cwi-dis/lissabon/python/sandbox/testlux.csv

requested | w_white | rgb_white | rgbw_white | rgb_r | rgb_g | rgb_b | w_lux | rgb_lux | rgbw_lux | w_cct | rgb_cct | rgbw_cct | parameter | value
0.0 | 0.065064 | 0.065019 | 0.065095 | 0.013901 | 0.009506 | 0.004196 | 19.44228 | 19.59958 | 19.59958 | 2511 | 2538 | 2524
0.0625 | 0.065049 | 0.065095 | 0.064958 | 0.013993 | 0.009567 | 0.004257 | 19.53666 | 19.72542 | 19.6625 | 2521 | 2545 | 2538
0.125 | 0.069169 | 0.068269 | 0.064408 | 0.01619 | 0.011307 | 0.005905 | 24.57026 | 23.31186 | 19.47374 | 2661 | 2790 | 2531
0.1875 | 0.077455 | 0.074586 | 0.06746 | 0.020645 | 0.015167 | 0.008988 | 35.3925 | 31.27124 | 23.50062 | 2871 | 3181 | 2698
0.25 | 0.087846 | 0.082399 | 0.070359 | 0.026352 | 0.020066 | 0.012955 | 48.66862 | 41.3699 | 28.03086 | 3026 | 3527 | 2906
0.3125 | 0.104891 | 0.095247 | 0.077134 | 0.035401 | 0.027909 | 0.019425 | 70.18726 | 57.54034 | 36.9655 | 3155 | 3921 | 3136
0.375 | 0.123964 | 0.109651 | 0.08365 | 0.045426 | 0.036515 | 0.026658 | 93.97102 | 75.28378 | 45.96306 | 3219 | 4205 | 3280
0.4375 | 0.149401 | 0.129046 | 0.090135 | 0.059037 | 0.048112 | 0.036133 | 126.3119 | 99.19338 | 54.77186 | 3291 | 4409 | 3394
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
