cwi-dis/lissabon/python/sb2/lux-2800-max.pdf

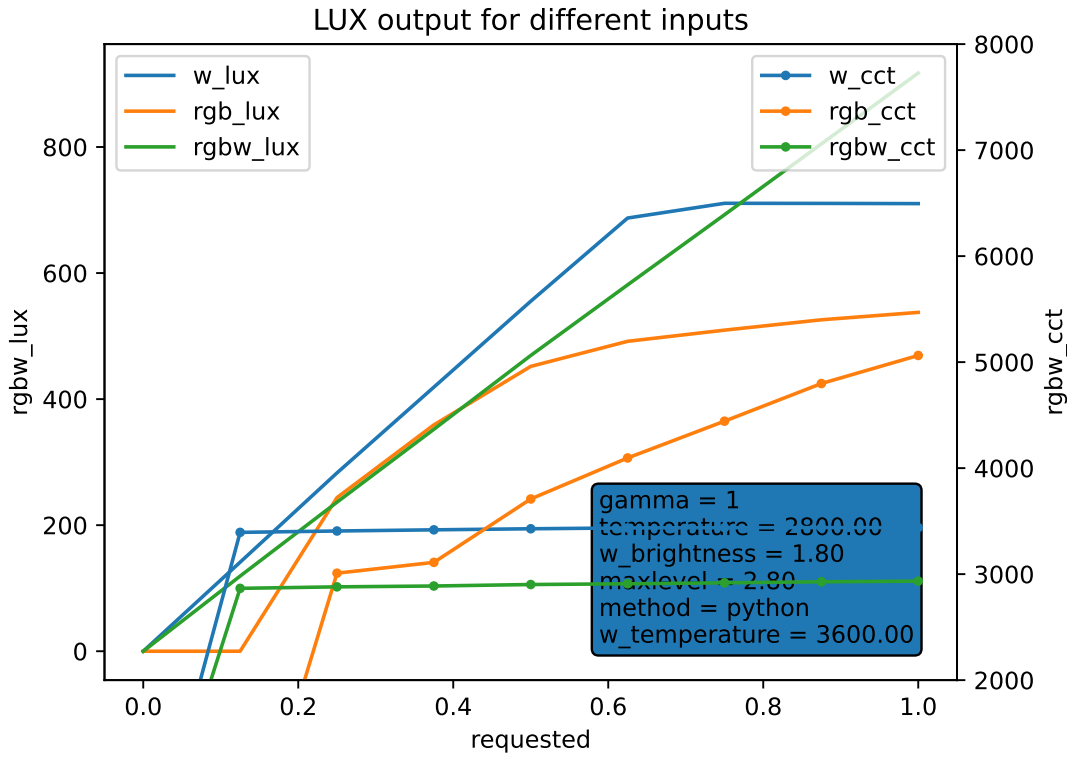
[picture p17: page 1]
requested; rgbw_lux; gamma = 1 temperature = 2800.00 w_brightness = 1.80 maxlevel = 2.80 method = python w_temperature = 3600.00; w_lux rgb_lux rgbw_lux; rgbw_cct; w_cct rgb_cct rgbw_cct

LUX output for different inputs
