cwi-dis/lissabon/python/sb2/lux-6500.pdf

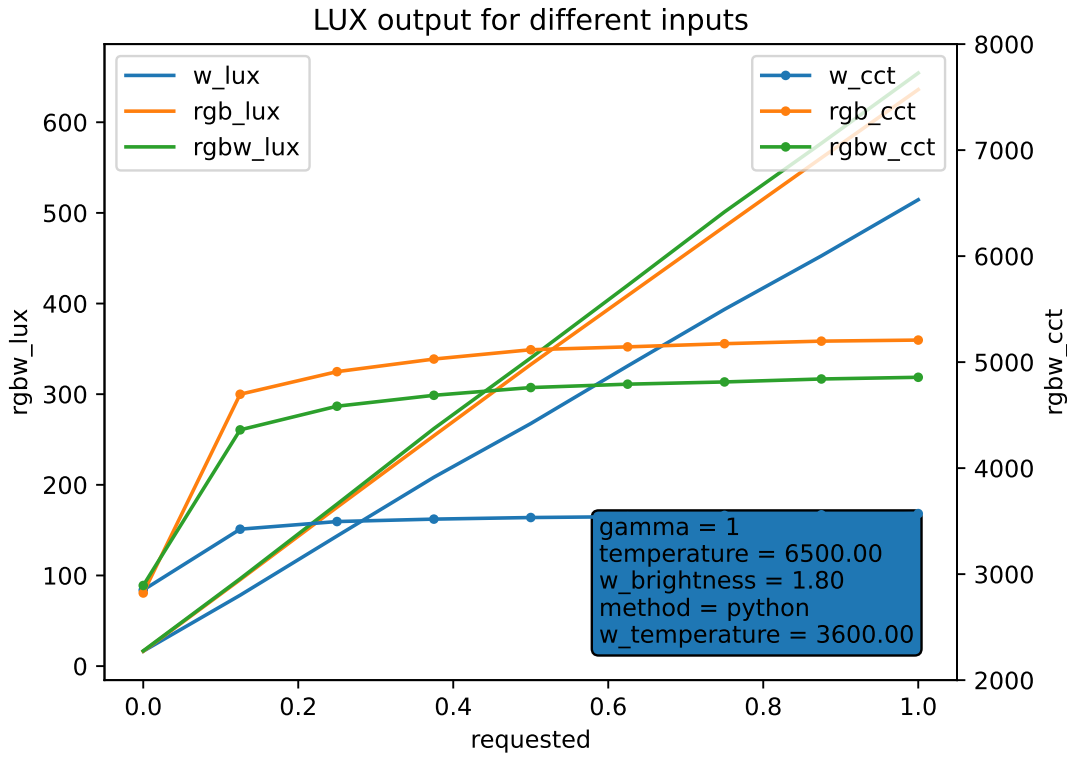
[picture p19: page 1]
requested; rgbw_lux; gamma = 1 temperature = 6500.00 w_brightness = 1.80 method = python w_temperature = 3600.00; w_lux rgb_lux rgbw_lux; rgbw_cct; w_cct rgb_cct rgbw_cct

LUX output for different inputs
