cwi-dis/lissabon/python/sb2/lux-correct.pdf

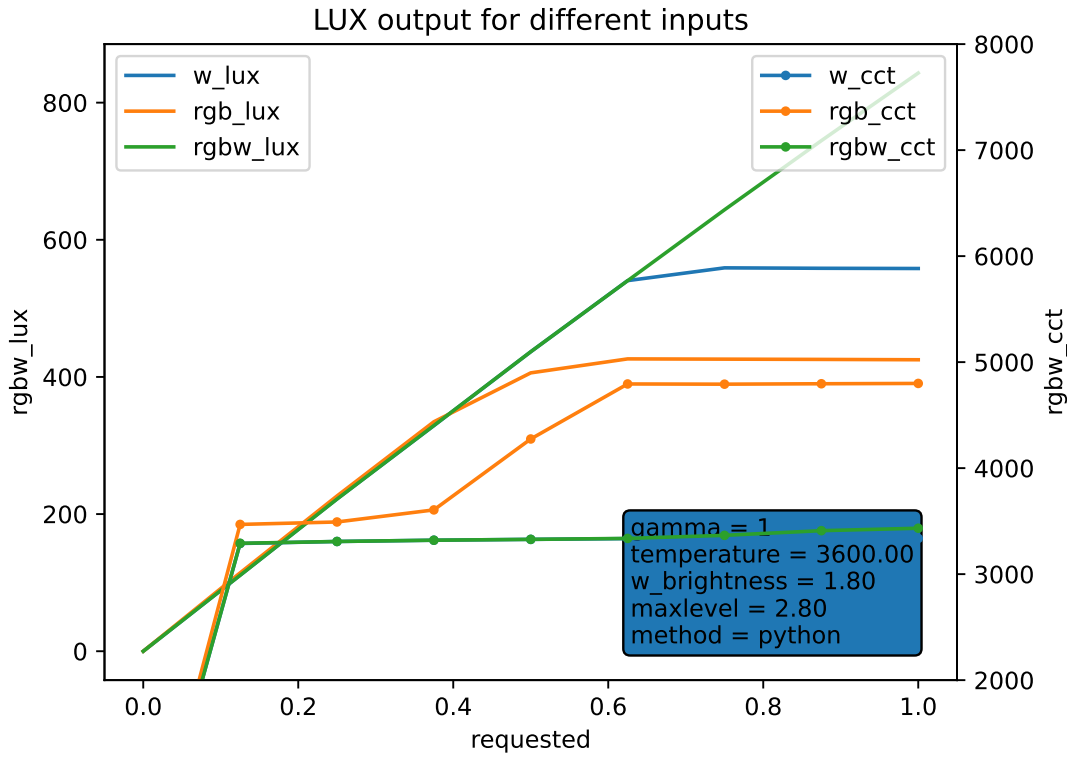
[picture p20: page 1]
requested; rgbw_lux; gamma = 1 temperature = 3600.00 w_brightness = 1.80 maxlevel = 2.80 method = python; w_lux rgb_lux rgbw_lux; rgbw_cct; w_cct rgb_cct rgbw_cct

LUX output for different inputs
