cwi-dis/lissabon/python/sb2/lux.pdf

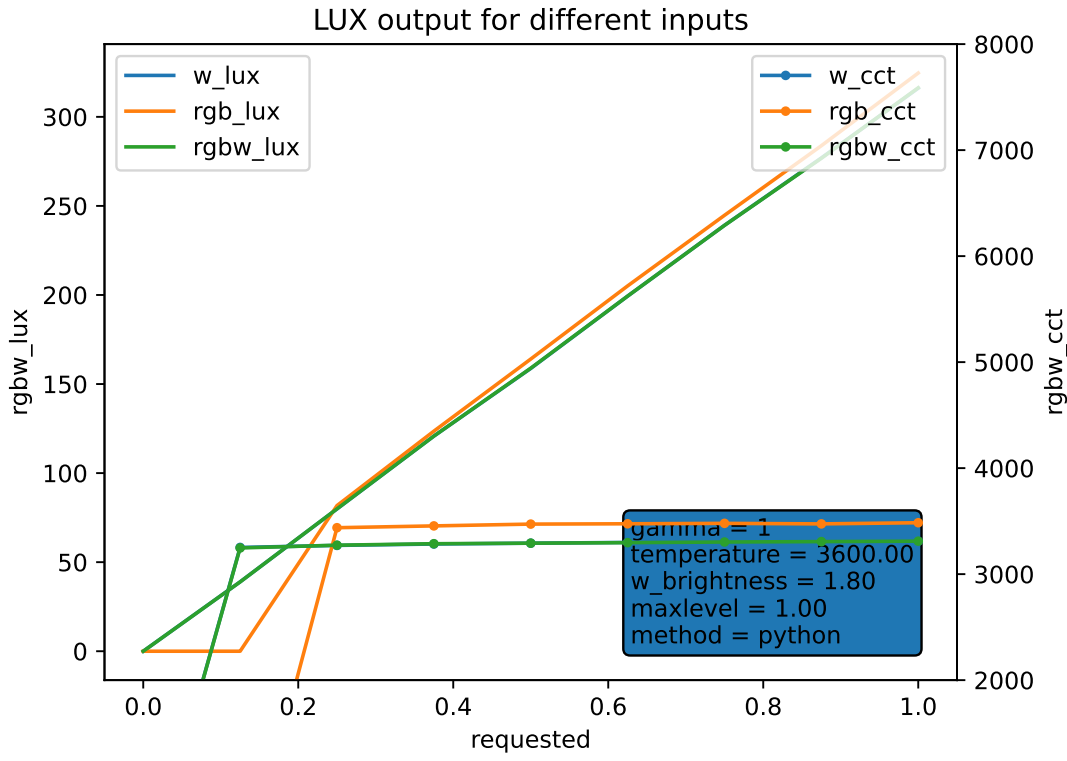
[picture p21: page 1]
requested; rgbw_lux; gamma = 1 temperature = 3600.00 w_brightness = 1.80 maxlevel = 1.00 method = python; w_lux rgb_lux rgbw_lux; rgbw_cct; w_cct rgb_cct rgbw_cct

LUX output for different inputs
