cwi-dis/lissabon/lissabonLedstrip/lissabonLedstrip.cpp

//
// A Neopixel strip server, which allows control over a strip of neopixels, intended
// to be used as lighting. Color can be set as fraction RGB or HSL, gamma can be changed,
// interval between lit pixels can be changed. Control is through a web UI or
// through REST calls (and/or, depending on Iotsa compile time options, COAP calls).
// The web interface can be disabled by building iotsa with IOTSA_WITHOUT_WEB.
//

#include "iotsa.h"
#include "iotsaConfigFile.h"
#include "LedstripDimmer.h"
#include "DimmerUI.h"

//
// Device can be rebooted or configuration mode can be requested by quickly tapping any button.
// TAP_DURATION sets the maximum time between press-release-press-etc.
#define TAP_COUNT_MODE_CHANGE 3
#define TAP_COUNT_REBOOT 6
#define TAP_DURATION 1000

// Enable Over The Air updates from ArduinoIDE. Needs at least 1MB flash.

// Define this to enable support for touchpads to control the led strip (otherwise only BLE/REST/WEB control)
#define WITH_TOUCHPADS

IotsaApplication application("Lissabon LEDstrip");

#ifdef IOTSA_WITH_BLE
#else
#warning Building this module without BLE support may be a bit pointless
#endif

#include "iotsaBattery.h"
#include "iotsaRunmode.h"
#define PIN_DISABLESLEEP 0
#define PIN_VBAT 35
#define VBAT_100_PERCENT (12.7/10.0) // 100K and 1M resistors divide by 11, not 10...
#define VBAT_0_PERCENT (10.5/10.0) // 100K and 1M resistors divide by 11, not 10...
IotsaBatteryMod batteryMod(application);

#include "iotsaPixelstrip.h"
IotsaPixelstripMod pixelstripMod(application);

#ifdef WITH_TOUCHPADS
#include "iotsaInput.h"
Touchpad upTouch(32, true, true, true);
Touchpad downTouch(13, true, true, true);
UpDownButtons levelEncoder(upTouch, downTouch, true);
Touchpad upTempTouch(14, true, true, true);
Touchpad downTempTouch(15, true, true, true);
UpDownButtons temperatureEncoder(upTempTouch, downTempTouch, false);
//Touchpad(15, true, false, true);

Input* inputs[] = {
  &levelEncoder,
  &temperatureEncoder
};

IotsaInputMod inputMod(application, inputs, sizeof(inputs)/sizeof(inputs[0]));
#endif // WITH_TOUCHPADS

#include "DimmerBLEServer.h"

using namespace Lissabon;

//
// LED Lighting module. 
//

class LissabonLedstripMod : public IotsaModule, public DimmerCallbacks
{
public:
  LissabonLedstripMod(IotsaApplication& _app)
  : IotsaModule(_app),
    dimmer(1, pixelstripMod, this),
#ifdef WITH_TOUCHPADS
    dimmerUI(dimmer),
#endif
    dimmerBLEServer(dimmer)
  {
  }
  void setup();
  void lateSetup() override;
  String info();
  void configLoad();
  void configSave();
  void loop();

protected:
  void dimmerOnOffChanged() override;
  void dimmerValueChanged() override;
  void dimmerAvailableChanged() override {};
  bool getHandler(const char *path, JsonObject& reply) override;
  bool putHandler(const char *path, const JsonVariant& request, JsonObject& reply) override;
private:
  void _tap();
  LedstripDimmer dimmer;
#ifdef WITH_TOUCHPADS
  DimmerUI dimmerUI;
#endif
  DimmerBLEServer dimmerBLEServer;
  void webHandler() override;

  uint32_t saveAtMillis = 0;
  uint32_t lastButtonChangeMillis = 0;
  int buttonChangeCount = 0;
};

void LissabonLedstripMod::_tap() {
  // Called whenever any button changed state.
  // Used to give visual feedback (led turning off) on presses and releases,
  // and to enable config mod after 4 taps and reboot after 8 taps
  uint32_t now = millis();
  if (now >= lastButtonChangeMillis + TAP_DURATION) {
    // Either the first change, or too late. Reset.
    if (lastButtonChangeMillis > 0) {
      IotsaSerial.println("TapCount: reset");
    }
    lastButtonChangeMillis = millis();
    buttonChangeCount = 0;
  }
  if (lastButtonChangeMillis > 0 && now < lastButtonChangeMillis + TAP_DURATION) {
    // A button change that was quick enough for a tap
    lastButtonChangeMillis = now;
    buttonChangeCount++;
    IFDEBUG IotsaSerial.printf("TapCount: %d\n", buttonChangeCount);
    iotsaStatus.setStatusPulse(IotsaStatus::COLOUR_WHITE, 100, 100, 200, "Tap");
    if (buttonChangeCount == TAP_COUNT_MODE_CHANGE) {
      IotsaSerial.println("TapCount: mode change");
      iotsaController.allowRequestedConfigurationMode();
    }
    if (buttonChangeCount == TAP_COUNT_REBOOT) {
      IotsaSerial.println("TapCount: reboot");
      iotsaStatus.setStatusPulse(IotsaStatus::COLOUR_WHITE, 500, 0, 500, "Rebooting");
      iotsaController.requestReboot(1000);
    }
  }
}

void LissabonLedstripMod::dimmerOnOffChanged() {
  _tap();

}
void
LissabonLedstripMod::webHandler() {
  IotsaWebServer *server = api.webService->server;
  bool anyChanged = false;
  anyChanged |= dimmer.formHandler_args(server, "ledstrip", true);

  if (anyChanged) {
    configSave();
    dimmer.updateDimmer();
  }
  
  
  String message = "<html><head><title>Lissabon Ledstrip</title></head><body><h1>Lissabon Ledstrip</h1>";
  message += "<h2>Settings</h2><form method='post'>";
  dimmer.formHandler_fields(message, "ledstrip", "ledstrip", false);
  message += "<input type='submit' name='set' value='Set Level'></form>";
  message += "<h2>Configuration</h2><form method='post'>";
  dimmer.formHandler_fields(message, "ledstrip", "ledstrip", true);
  message += "<input type='submit' name='set' value='Update Configuration'></form>";
  message += "</body></html>";
  server->send(200, "text/html", message);
  iotsaController.extendCurrentMode();
}

String LissabonLedstripMod::info() {
  // Return some information about this module, for the main page of the web server.
  String message = "<p>";
  message += dimmer.info();
  message += "See <a href=\"/ledstrip\">/ledstrip</a> for setting the LEDstrip level and temperature.";
#ifdef IOTSA_WITH_REST
  message += " Or use REST api at <a href='/api/ledstrip'>/api/ledstrip</a>.";
#endif
#ifdef IOTSA_WITH_BLE
  message += " Or use BLE service " + String(Lissabon::serviceUUIDstring) + ".";
#endif
  message += "</p>";
  return message;
}

bool LissabonLedstripMod::getHandler(const char *path, JsonObject& reply) {
  dimmer.getHandler(reply);
  iotsaController.extendCurrentMode();
  return true;
}

bool LissabonLedstripMod::putHandler(const char *path, const JsonVariant& request, JsonObject& reply) {
  bool anyChanged = false;
  JsonObject reqObj = request.as<JsonObject>();
  if (!reqObj) return false;
  if (dimmer.putHandler(reqObj)) anyChanged = true;
  if (anyChanged) {
    // Should do this only for configuration changes
    configSave();
  }
  if (anyChanged) dimmer.updateDimmer(); // xxxjack or is this called already?
  iotsaController.extendCurrentMode();
  return anyChanged;

}
void LissabonLedstripMod::lateSetup() {
  name = "ledstrip";
  // /ledstrip (the module page, GET + POST) is auto-registered by this
  // get=true api.setup(); it dispatches to webHandler().
  api.setup("ledstrip", true, true);
}

void LissabonLedstripMod::configLoad() {
  IotsaConfigFileLoad cf("/config/ledstrip.cfg");
  dimmer.configLoad(cf, "ledstrip");
}

void LissabonLedstripMod::configSave() {
  IotsaConfigFileSave cf("/config/ledstrip.cfg");
  dimmer.configSave(cf, "ledstrip");
}

void LissabonLedstripMod::setup() {
  // Allow switching the dimmer to iotsa config mode over BLE or with taps
  batteryMod.allowBLEConfigModeSwitch();
#ifdef IOTSA_WITH_BLE
  // Wires this appliance's identify (blink) into the generic core runmode
  // BLE identify command, so DimmerBLEClient's identify() -- which now goes
  // through IotsaRunmodeBLEClient, not Lissabon's own identifyUUID -- has
  // something to actually trigger here.
  if (IotsaRunmodeMod::instance()) IotsaRunmodeMod::instance()->addIdentifyCallback([this]() { dimmer.identify(); });
#endif
#ifdef PIN_VBAT
  batteryMod.setPinVBat(PIN_VBAT, VBAT_100_PERCENT, VBAT_0_PERCENT);
#endif
#ifdef PIN_DISABLESLEEP
  batteryMod.setPinDisableSleep(PIN_DISABLESLEEP);
#endif
  configLoad();
#ifdef WITH_TOUCHPADS
  iotsaController.allowRCMDescription("tap any touchpad 4 times");
  dimmerUI.setUpDownButtons(levelEncoder);
  dimmerUI.setTemperatureUpDownButtons(temperatureEncoder);
#endif
  dimmer.setup();
  dimmerBLEServer.setup();
  dimmer.updateDimmer();
}

void LissabonLedstripMod::dimmerValueChanged() {
  iotsaController.postponeSleep(2000);
  saveAtMillis = millis() + 1000;
}

void LissabonLedstripMod::loop() {
  // See if we have a value to save (because the user has been turning the dimmer)
  if (saveAtMillis > 0 && millis() > saveAtMillis) {
    saveAtMillis = 0;
    IFDEBUG IotsaSerial.println("save ledstrip config");
    configSave();
  }
  dimmer.loop();
}

// Instantiate the Led module, and install it in the framework
LissabonLedstripMod ledstripMod(application);

// Standard setup() method, hands off most work to the application framework
void setup(void){
  application.setup();
  application.lateSetup();
}

// Standard loop() routine, hands off most work to the application framework
void loop(void){
  application.loop();
}
