cwi-dis/lissabon/lissabonController/display.cpp

#include "iotsa.h"
#include "display.h"

#include <Wire.h>
#include "Adafruit_GFX.h"
#include "Adafruit_SSD1306.h"
#define PIN_SDA 5
#define PIN_SCL 4
#define OLED_WIDTH 128
#define OLED_HEIGHT 64
#define DISPLAY_WIDTH 64
#define DISPLAY_HEIGHT 128
static Adafruit_SSD1306 *oled;

#define STRIPS_X 2
#define STRIPS_Y 2
#define STRIPS_HEIGHT 12
#define STRIPS_WIDTH 62
#define ICON_HEIGHT on_height
#define ICON_WIDTH on_width
#define LABEL_WIDTH (STRIPS_WIDTH-ICON_WIDTH-2)
#define LABEL_X (ICON_WIDTH+STRIPS_X)
#define ICON_X 0
#define ICON_Y (-2)
#define N_STRIPS 7

#define SEPARATOR_Y (STRIPS_Y+STRIPS_HEIGHT*N_STRIPS+2)
#define SEPARATOR_WIDTH 64
#define LEVEL_X 16
#define LEVEL_Y (SEPARATOR_Y+3)
#define LEVEL_WIDTH 33
#define LEVEL_HEIGHT 12
#define TEMP_X 16
#define TEMP_Y (LEVEL_Y + LEVEL_HEIGHT+2)
#define TEMP_WIDTH 33
#define TEMP_HEIGHT 12
#define ACTIVITY_X 0
#define ACTIVITY_Y (TEMP_Y + LEVEL_HEIGHT+2)
#define ACTIVITY_WIDTH STRIPS_WIDTH
#define ACTIVITY_HEIGHT 8

#include "icons/on.h"
#include "icons/off.h"
#include "icons/sun.h"
#include "icons/lightbulb.h"
#include "icons/question.h"
#include "icons/dots.h"
#include "icons/arrow.h"
#include "icons/doublearrow.h"

Display::Display()
{
  Wire.begin(PIN_SDA, PIN_SCL);
  oled = new Adafruit_SSD1306(OLED_WIDTH, OLED_HEIGHT, &Wire, -1);
  if (!oled->begin(SSD1306_SWITCHCAPVCC, 0x3c, false, false)) {
    IFDEBUG IotsaSerial.println("OLED init failed");
    return;
  }
  oled->clearDisplay();
  oled->setRotation(1);
  oled->setTextSize(1);
  oled->setTextColor(WHITE);
  oled->setTextWrap(false);
  oled->dim(false);

  oled->drawFastHLine(0, SEPARATOR_Y, SEPARATOR_WIDTH, WHITE);

  oled->drawXBitmap(LEVEL_X-off_width, LEVEL_Y, off_bits, off_width, off_height, WHITE);
  oled->drawRect(LEVEL_X, LEVEL_Y, LEVEL_WIDTH, LEVEL_HEIGHT, WHITE);
  oled->drawXBitmap(LEVEL_X+LEVEL_WIDTH+1, LEVEL_Y, on_bits, on_width, on_height, WHITE);
#ifdef DIMMER_WITH_TEMPERATURE
  oled->drawXBitmap(TEMP_X-off_width, TEMP_Y, lightbulb_bits, lightbulb_width, lightbulb_height, WHITE);
  oled->drawRect(TEMP_X, TEMP_Y, TEMP_WIDTH, TEMP_HEIGHT, WHITE);
  oled->drawXBitmap(TEMP_X+TEMP_WIDTH+1, TEMP_Y, sun_bits, sun_width, sun_height, WHITE);
#endif
  oled->display();
}

void Display::flash() {
  oled->fillRect(0, 0, DISPLAY_WIDTH, DISPLAY_HEIGHT, INVERSE);
  oled->display();
  delay(200);
  oled->fillRect(0, 0, DISPLAY_WIDTH, DISPLAY_HEIGHT, INVERSE);
  oled->display();
}

void Display::dim(bool _dim) {
  oled->dim(_dim);
}

void Display::clearStrips() {
  // xxxjack clear strip area
  // xxxjack show all in 0
  oled->fillRect(0, 0, DISPLAY_WIDTH, STRIPS_HEIGHT*N_STRIPS+4, BLACK);
  //addStrip(0, "ALL", true);
  selectedStripOnDisplay = -1;
}

void Display::addStrip(int index, String name, StripStatus status) {
  // xxxjack show name in index
  int x = LABEL_X;
  int y = STRIPS_Y + index*STRIPS_HEIGHT;
  oled->fillRect(0, y, DISPLAY_WIDTH, STRIPS_HEIGHT+2, BLACK);
  oled->setCursor(x, y);
  oled->print(name.c_str());
  // "synced" (have valid data, idle) is the normal/healthy steady state, so it's
  // drawn blank -- every other state gets a distinct icon, on/off are reserved for
  // the level slider above and not reused here (see StripStatus in display.h).
  if (status == StripStatus::connected) {
    oled->drawXBitmap(ICON_X, y+ICON_Y, doublearrow_bits, doublearrow_width, doublearrow_height, WHITE);
  } else if (status == StripStatus::connecting) {
    oled->drawXBitmap(ICON_X, y+ICON_Y, arrow_bits, arrow_width, arrow_height, WHITE);
  } else if (status == StripStatus::seen) {
    oled->drawXBitmap(ICON_X, y+ICON_Y, dots_bits, dots_width, dots_height, WHITE);
  } else if (status == StripStatus::unavailable) {
    oled->drawXBitmap(ICON_X, y+ICON_Y, question_bits, question_width, question_height, WHITE);
  } else {
    // synced: draw nothing
  }
}

void Display::selectStrip(int index) {
  // xxxjack clear ring around selected
  if (selectedStripOnDisplay >= 0) {
    int x = LABEL_X-2;
    int y = STRIPS_Y + selectedStripOnDisplay*STRIPS_HEIGHT - 2;
    oled->drawRoundRect(x, y, LABEL_WIDTH+4, STRIPS_HEIGHT, 3, BLACK);
  }

  selectedStripOnDisplay = index;
  if (selectedStripOnDisplay >= 0) {
    // xxxjack draw ring around selected
    int x = LABEL_X-2;
    int y = STRIPS_Y + selectedStripOnDisplay*STRIPS_HEIGHT - 2;
    oled->drawRoundRect(x, y, LABEL_WIDTH+4, STRIPS_HEIGHT, 3, WHITE);
  }
}

void Display::clearLevel() {
  oled->fillRect(LEVEL_X, LEVEL_Y, LEVEL_WIDTH, LEVEL_HEIGHT, BLACK);
}

void Display::setLevel(float level, bool on, float wantedLevel) {
  clearLevel();
  oled->drawRect(LEVEL_X, LEVEL_Y, LEVEL_WIDTH, LEVEL_HEIGHT, WHITE);
  if (on) {
    oled->fillRect(LEVEL_X, LEVEL_Y, int(level*LEVEL_WIDTH), LEVEL_HEIGHT, WHITE);
  } else {
    oled->drawFastVLine(LEVEL_X+int(level*LEVEL_WIDTH), LEVEL_Y, LEVEL_HEIGHT, WHITE);
  }
  if (wantedLevel >= 0) {
    int wantedLPos = int(wantedLevel*(LEVEL_WIDTH-2));
    oled->drawFastHLine(LEVEL_X+1, LEVEL_Y+1, wantedLPos, WHITE);
    oled->drawFastHLine(LEVEL_X+1+wantedLPos, LEVEL_Y+1, LEVEL_WIDTH-1-wantedLPos, BLACK);
  }
}

void Display::clearTemp() {
#ifdef DIMMER_WITH_TEMPERATURE
  // xxxjack clear color area
  oled->fillRect(TEMP_X, TEMP_Y, TEMP_WIDTH, TEMP_HEIGHT, BLACK);
#endif
}

void Display::setTemp(float color) {
#ifdef DIMMER_WITH_TEMPERATURE
  clearTemp();
  oled->drawRect(TEMP_X, TEMP_Y, TEMP_WIDTH, TEMP_HEIGHT, WHITE);
  int tempPos = int(color*TEMP_WIDTH);
  if (tempPos <= 0) tempPos = 1;
  if (tempPos >= TEMP_WIDTH-1) tempPos = TEMP_WIDTH-2;
  oled->drawFastVLine(TEMP_X+tempPos, TEMP_Y, TEMP_HEIGHT, WHITE);
#endif
}

void Display::showScanning(bool _isScanning) {
  if (_isScanning == isScanning) return;
  isScanning = _isScanning;
  _updateActivity(isScanning ? "scanning" : "");
}

void Display::showActivity(const char *activity) {
  isScanning = false;
  _updateActivity(activity);
}

void Display::_updateActivity(const char *activity) {
  oled->fillRect(ACTIVITY_X, ACTIVITY_Y, ACTIVITY_WIDTH, ACTIVITY_HEIGHT, BLACK);
  oled->setCursor(ACTIVITY_X, ACTIVITY_Y);
  if (activity && activity[0]) oled->print(activity);
}

void Display::show() {
  oled->display();
}
