cwi-dis/lissabon/libLissabon/src/LissabonBLE.h

#ifndef _LISSABONBLE_H_
#define _LISSABONBLE_H_
#ifdef IOTSA_WITH_BLE
#include "iotsaBLE.h"

namespace Lissabon {
// UUID of service advertised by iotsaLedstrip and iotsaDimmer devices
extern NimBLEUUID serviceUUID;
extern const char* serviceUUIDstring;
//extern const char* serviceUUID2901;
//extern const uint8_t serviceUUID2904format;
//extern const uint16_t serviceUUID2904unit;

extern NimBLEUUID isOnUUID;
extern const char* isOnUUIDstring;
extern const char* isOnUUID2901;
extern const uint8_t isOnUUID2904format;
extern const uint16_t isOnUUID2904unit;
typedef uint8_t Type_isOn;

extern NimBLEUUID brightnessUUID;
extern const char* brightnessUUIDstring;
extern const char* brightnessUUID2901;
extern const uint8_t brightnessUUID2904format;
extern const uint16_t brightnessUUID2904unit;
typedef uint16_t Type_brightness;

extern NimBLEUUID temperatureUUID;
extern const char* temperatureUUIDstring;
extern const char* temperatureUUID2901;
extern const uint8_t temperatureUUID2904format;
extern const uint16_t temperatureUUID2904unit;
typedef uint16_t Type_temperature;

};
#endif // IOTSA_WITH_BLE
#endif // _LISSABONBLE_H_
